ekoslav/ESP32_Password_keyboard/Images/breadboard_1.jpg

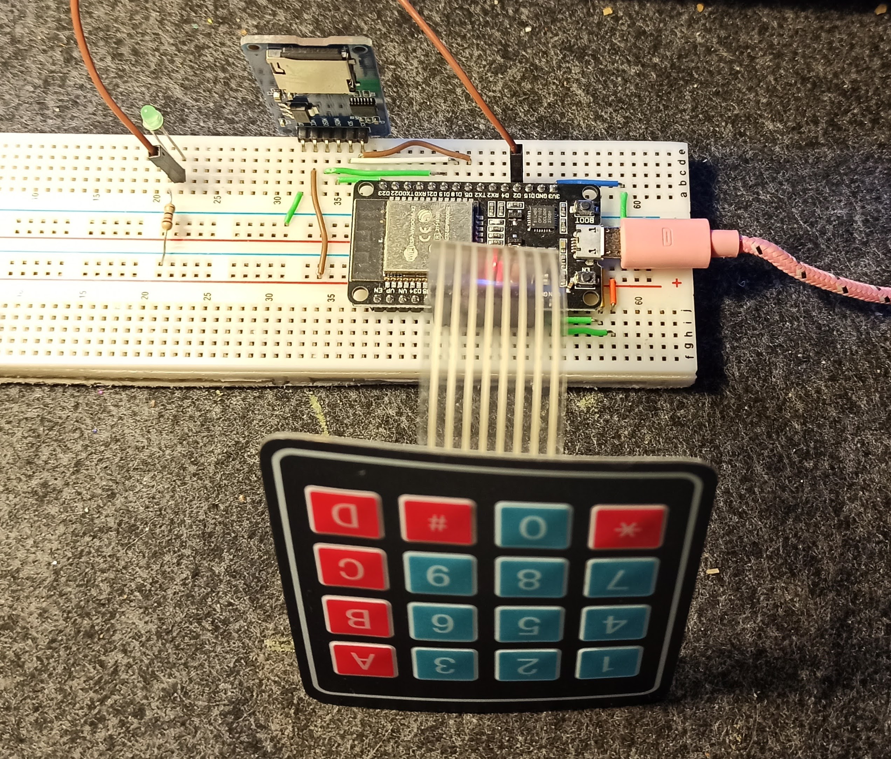
Images/breadboard_1.jpg
