ekoslav/ESP32_Password_keyboard/Images/breadboard_2.jpg

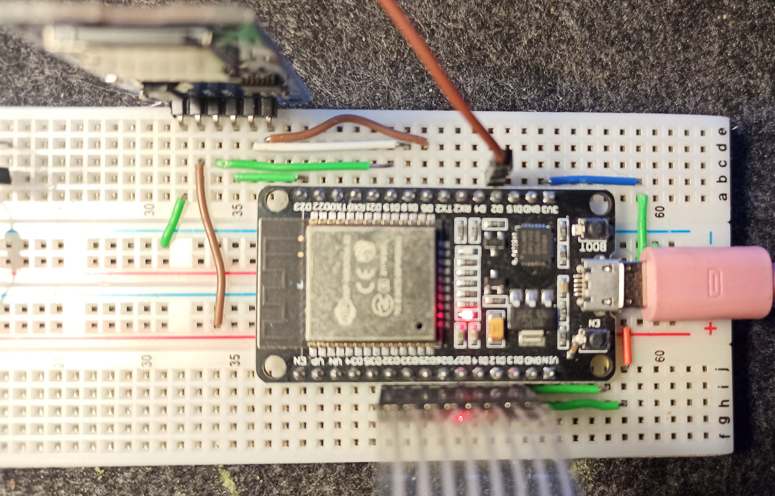
Images/breadboard_2.jpg
