ekoslav/ESP32_Password_keyboard/Images/Inside_SD_card_reader.jpg

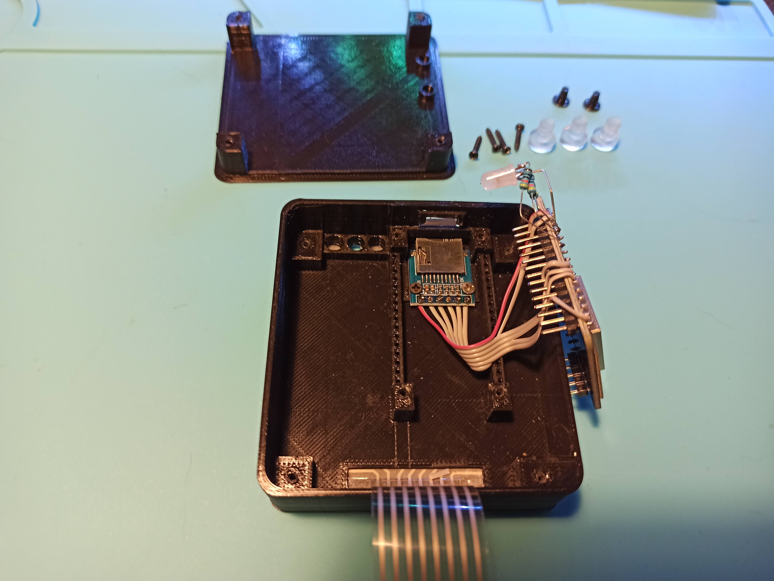
Images/Inside_SD_card_reader.jpg
